dp-web4/CellCPU/SYNCHRONISM_PRINCIPLES.md

# CellCPU - Synchronism Principles in Silicon

**Platform**: ATtiny45 (8-bit AVR, 4KB flash, 256B RAM)
**Role**: Autonomous cell agent demonstrating distributed intelligence at smallest scale

---

## Overview

CellCPU embodies [Synchronism](https://github.com/dp-web4/Synchronism)'s core principles in embedded hardware. Each battery cell operates as an **autonomous agent** with local decision-making, demonstrating that distributed intelligence doesn't require powerful processors - it's a fundamental architectural pattern that scales from philosophy to 8-bit microcontrollers.

---

## Core Synchronism Principles Demonstrated

### 1. Scale-Based Autonomy

**Principle**: Each scale operates autonomously within its Markov blanket

**CellCPU Implementation**:
```
CELL SCALE (ATtiny45)
├─ Autonomous Decisions:
│  ├─ When to sample temperature/voltage
│  ├─ How to interpret sensor readings
│  ├─ Whether to activate balancing FET
│  └─ Error detection and local handling
│
├─ Local State Machine:
│  ├─ IDLE → MEASURING → TRANSMITTING → IDLE
│  ├─ Cell controls its own timing
│  └─ No external micromanagement
│
└─ Interface (Markov Blanket):
   └─ VUART: Only processed results cross boundary
```

**Key Insight**: ModuleCPU doesn't tell the cell *how* to measure temperature or *when* to sample. The cell makes these decisions autonomously. ModuleCPU only requests results and receives them through the Markov blanket interface.

---

### 2. Markov Blankets Create Hierarchical Autonomy

**Principle**: Each entity's interface defines its reality and hides internal complexity

**CellCPU's Markov Blanket**:

```
EXTERNAL WORLD                    MARKOV BLANKET                 INTERNAL WORLD
(ModuleCPU's view)                (VUART Interface)              (Cell's hidden state)

                                  ┌──────────────┐
Temperature Request      ────────>│              │
                                  │    VUART     │────> State machine: IDLE→MEASURE
                                  │   20kbps     │
                                  │              │<──── I2C: Read MCP9843
Temperature=23.5°C       <────────│              │
                                  │              │<──── ADC: Read cell voltage
                                  └──────────────┘
                                                  └──── Compute: Apply calibration
ModuleCPU CANNOT see:                            └──── Decision: Activate balancing?
  - I2C communication timing
  - ADC sampling strategy
  - Internal state machine states
  - Sensor fusion algorithms
  - Error detection logic
```

**Markov Blanket = Interface**:
- **Incoming**: Commands from ModuleCPU (implicit in VUART timing)
- **Outgoing**: Temperature, voltage, status flags
- **Hidden**: Everything else (I2C, ADC, decision logic)

---

### 3. Each Scale is "God" to Subordinates

**Principle**: Higher scales provide context and constraints without micromanaging

**For CellCPU**:
```
MODULECPU (God to Cell)
├─ Provides:
│  ├─ Power (cell voltage)
│  ├─ Communication protocol (VUART timing)
│  └─ Context: "You are cell #5 in this module"
│
├─ Requests:
│  ├─ Periodic data (temp/voltage)
│  └─ Compliance with protocol
│
└─ Does NOT control:
   ├─ HOW cell measures temperature
   ├─ WHEN cell samples ADC (internally)
   ├─ HOW cell interprets readings
   └─ Internal state transitions
```

**Cell's Reality**:
- Cell doesn't know about Pack Controller
- Cell doesn't know about CAN bus
- Cell doesn't know it's 1 of 2,944 cells in a pack (32 modules × 92 cells)
- **Cell's universe = ModuleCPU + adjacent cells in VUART daisy-chain**

This is **scale-specific reality** - the cell operates in a smaller universe than the module, which operates in a smaller universe than the pack.

---

### 4. Distributed Intelligence (No Central Control)

**Principle**: Intelligence emerges from local decisions, not central planning

**CellCPU's Local Intelligence**:

#### Temperature Monitoring
```c
// Cell decides HOW to monitor (not dictated by ModuleCPU)
void MonitorTemperature(void) {
    int16_t temp = ReadMCP9843();

    // Local decision: Is this reading anomalous?
    if (abs(temp - g_last_temp) > ANOMALY_THRESHOLD) {
        // Local intelligence: Resample to verify
        _delay_ms(100);
        temp = ReadMCP9843();
    }

    // Local decision: Apply calibration
    temp += g_calibration_offset;

    g_current_temp = temp;
}
```

#### Balancing Control
```c
// Cell decides WHEN to balance (local autonomy)
void UpdateBalancing(void) {
    uint16_t voltage = ReadCellVoltage();

    // Local decision logic
    if (voltage > BALANCE_THRESHOLD && !g_balancing_active) {
        // Activate balancing FET
        PORTB |= (1 << BALANCE_FET_PIN);
        g_balancing_active = true;
    } else if (voltage < BALANCE_STOP_THRESHOLD && g_balancing_active) {
        // Deactivate balancing FET
        PORTB &= ~(1 << BALANCE_FET_PIN);
        g_balancing_active = false;
    }
}
```

**No Central Balancing Controller**:
- Each cell decides when to balance based on local voltage
- ModuleCPU aggregates but doesn't centralize balancing logic
- System-level balancing *emerges* from 92 autonomous cell decisions

---

### 5. Sensor Fusion Creates Reality

**Principle**: Reality emerges from weighted fusion of multiple sensors across time

**CellCPU as Reality Sensor**:

```
TEMPORAL SENSORS (across time)
├─ Temperature (MCP9843)
│  └─ "What is the thermal state NOW?"
│
├─ Voltage (ADC)
│  └─ "What is the electrochemical state NOW?"
│
└─ Historical Readings (memory)
   └─ "What was the state THEN?"

SENSOR FUSION ↓

EMERGENT REALITY: "Cell Health"
├─ Temperature trend: Rising/stable/falling?
├─ Voltage trend: Charging/discharging/balanced?
├─ Correlation: Does temp track with voltage as expected?
└─ EMERGENT CONCEPT: "This cell is healthy" or "This cell is degraded"
```

**Multi-Scale Sensor Fusion**:
```
CELL LEVEL
92 cells × (temp + voltage) = 184 temporal sensors
    ↓ (fusion at module level)

MODULE LEVEL
32 modules × (aggregated cell data) = 32 module sensors
    ↓ (fusion at pack level)

PACK LEVEL
1 pack × (aggregated module data) = emergent "pack health"
```

**Reality is Fractal**:
- Cell fuses temp+voltage → "cell state"
- Module fuses 92 cells → "module state"
- Pack fuses 32 modules → "pack state"
- **Same fusion algorithm at each scale, different inputs**

---

### 6. Intent Dynamics

**Principle**: Reality responds to intent; intent propagates through scales

**Battery as Metabolic System**:

```
USER INTENT: "Charge the battery"
    ↓
PACK CONTROLLER: Closes charging relay
    ↓
MODULES: Current flows, voltage rises
    ↓
CELLS: Detect rising voltage
    ↓
CELLCPU: Measures voltage increase
    ↓
LOCAL INTENT: "Balance if voltage too high"
    ↓
BALANCING FET: Activates to dissipate excess energy
```

**Intent Flow is Bidirectional**:
- **Top-down**: Pack enables charging → Cells experience voltage rise
- **Bottom-up**: Cell detects overcharge → Balances → Module adjusts → Pack responds

**CellCPU's Local Intent**:
```c
// Cell has its own intent: "Maintain safe operating conditions"
void CellMainLoop(void) {
    while (1) {
        // INTENT: Know my state
        UpdateSensors();

        // INTENT: Protect myself
        if (OverTemperature()) {
            // Local protective intent
            DisableBalancing();
            SetErrorFlag();
        }

        // INTENT: Communicate state
        if (TimeToTransmit()) {
            TransmitStatus();
        }

        // INTENT: Respond to environment
        if (VoltageImbalanced()) {
            ActivateBalancing();
        }
    }
}
```

---

## Philosophical Implications

### 1. Consciousness Doesn't Require Complexity

**Insight**: Even an ATtiny45 with 4KB flash demonstrates autonomous agency

- Cell "knows" its state (sensor readings)
- Cell "decides" when to act (balancing, error flags)
- Cell "communicates" with its environment (VUART)
- Cell operates within its Markov blanket (limited but complete reality)

**This is a primitive form of consciousness** - not human-like, but agency nonetheless.

### 2. Scale Invariance of Intelligence

**Principle**: The same intelligence patterns appear at every scale

| Scale | Entity | Sensors | Decisions | Interface |
|---|---|---|---|---|
| **Cosmic** | Universe | Physical laws | Quantum events | Spacetime |
| **Biological** | Cell | Receptors | Gene expression | Cell membrane |
| **Neural** | Neuron | Dendrites | Action potential | Synapse |
| **Battery** | CellCPU | Temp/voltage | Balancing | VUART |
| **Digital** | Bit | Transistor state | Logic gates | Wire |

**Same pattern, different substrate** - CellCPU is isomorphic to biological cells, neurons, and even cosmic-scale dynamics.

### 3. Emergence Through Hierarchy

**From 92 Dumb Cells → 1 Smart Module**:
```
Individual cell: Simple logic (temp > threshold? → balance)
    ↓ (92 cells coordinated by module)
Emergent module behavior: Sophisticated balancing strategy
    ↓ (32 modules coordinated by pack)
Emergent pack behavior: Optimal charge/discharge management
```

**Intelligence emerges** not from making individual cells smarter, but from hierarchical coordination of simple autonomous agents.

### 4. Trust as Structural Property

**Synchronism Insight**: Trust isn't added on top - it emerges from structure

**CellCPU's Structural Trust**:
- **Physical binding**: Serial number in flash (unforgeable at manufacturing)
- **Witnessed presence**: ModuleCPU observes cell via VUART (proves existence)
- **Consistent behavior**: Reliable communication builds temperament (emergent trust)
- **Sensor fusion**: Multiple readings over time create veracity (data integrity)

**Trust isn't a feature** - it's a property of the hierarchical structure itself.

---

## Links to Synchronism Whitepaper

This implementation demonstrates concepts from specific sections of the [Synchronism Whitepaper](https://github.com/dp-web4/Synchronism/blob/main/whitepaper.md):

- **Section 1.0**: Intent dynamics (cell intent → balancing action)
- **Section 2.0**: Markov blankets (VUART as cell's interface boundary)
- **Section 3.0**: Hermetic Principles (As above, so below - same patterns at all scales)
- **Section 4.0**: Scale-based autonomy (cell autonomy within module context)
- **Section 5.0**: Reality as sensor fusion (temp + voltage → cell health)

---

## Code as Philosophy

**Every line of CellCPU code is a philosophical statement**:

```c
// "I exist autonomously"
void main(void) {
    InitializeHardware();

    // "I have agency within my Markov blanket"
    while (1) {
        // "I sense reality"
        UpdateSensors();

        // "I make decisions"
        UpdateState();

        // "I act on my intent"
        UpdateActuators();

        // "I communicate my reality"
        TransmitStatus();
    }
}
```

**This is Synchronism in silicon** - proof that distributed intelligence, Markov blankets, and scale-based autonomy aren't just abstractions, but functional design principles that work in 256 bytes of RAM.

---

**From cosmic intent to 8-bit microcontroller: The same principles govern reality at every scale.**
