dp-web4/CellCPU/.github/TOPICS.md

# Repository Topics

## Primary Topics
- battery-management-system
- bms
- embedded-systems
- modbatt
- battery

## Platform/Hardware
- attiny45
- avr
- cell-monitoring
- 8-bit-microcontroller

## Architecture/Patterns
- distributed-intelligence
- hierarchical-control
- autonomous-control
- daisy-chain
- virtual-uart

## Application Domain
- electric-vehicle
- lithium-ion
- energy-storage
- iot
- balancing

## Ecosystem/Framework
- web4
- synchronism
- open-source
- agpl-3.0

## Use these topics on GitHub via Settings → Topics
